iot-lab/catimex-power-monitoring/legacy/v0.1/boards/pcb/lmp2011/README.md

#PCB eagle schematics and boards for LMP2011

El LMP2011 es un OP AMP auto-zero de offset de entrada de 60uV máximo (en todo rango de temperatura) y 0.8 uV tipicos. Ademas tiene un CMRR tipico de 130dB con un minimo de  95dB.

### Cómo usar

Considerando que se tiene una placa compatible con RIOT:

- Conectar los controles de switch (SWITCH_CTRL_1 a SWITCH_CTRL_5) a GPIO.
- Conectar las salidas de low current, high current y adc volt (medición de supply) a las entradas analógicas.
- Conectar alimentación a entrada micro USB desde computadora o 5V.
- Conectar alimentación del MCU objetivo a VBAT. En caso de querer alimentar todo desde la alimentación USB, conectar un jumper entre 5V y VBAT.
- Si el MCU objetivo puede ser conectado por USB, utilizar el puerto USB tipo A. Este puerto mantiene la comunicación serial.
- En caso de no poder utilizar un USB, la alimentación del MCU objetivo puede obtenerse desde VMCU.

### Especificaciones:
- Alimentación de 5V desde USB
- Rango: ~10uA - 50mA
- Primera etapa ganancia de 100
- Segunda etapa amplifica 197 para bajas corrientes y 1.51 para altas corrientes.

### Working of current version (2) (detailed)

El funcionamiento de este circuito es equivalente al del MAX4239, sólo que sin un DC booster (falta verificar que efectivamente este no sea necesario).

La primera etapa se encarga de amplificar el voltage en la resistencia de Shunt mediante configuracion de amplificador diferencial. Las resistencias R1,R2,R4 y R5 conforman una ganancia diferencial de 100 (100k/1k) entre VBAT y VS- (terminales de la resistencia de shunt). R6 y C3 son añadidos para estabilidad, C3 además ayuda a disminuir los peaks de carga del auto-zero. C2 ayuda a mantener la fuente estable.

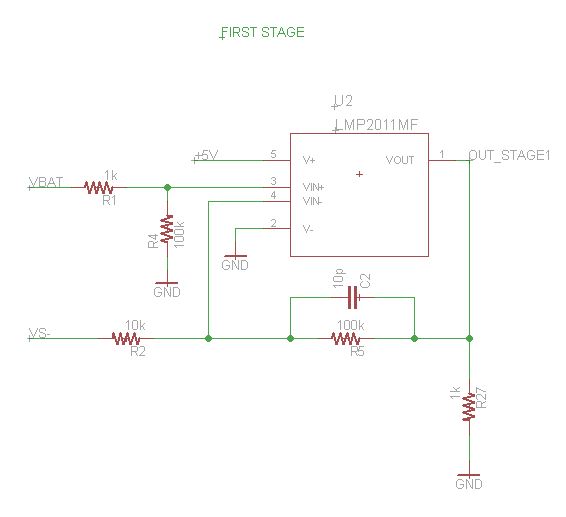
[picture p3: v0.1/boards/pcb/lmp2011/images/first.JPG]


La segunda etapa es conformada por un DUAL OP AMP LTC6241 de alta precision. Hay dos rangos de medicion que tienen distintas ganancias cada uno:
- Low current range: 0uA-600uA
- High current tange: 600uA-50mA

Para corrientes bajas, la segunda etapa amplifica x197. Para corrientes altas solo se amplifica x1.51. Estas ganancias acomodan el voltaje a los rangos del ADC. Las resistencias de 49.9R son utiles para aislar la salida del amplificador y evitar oscilaciones.

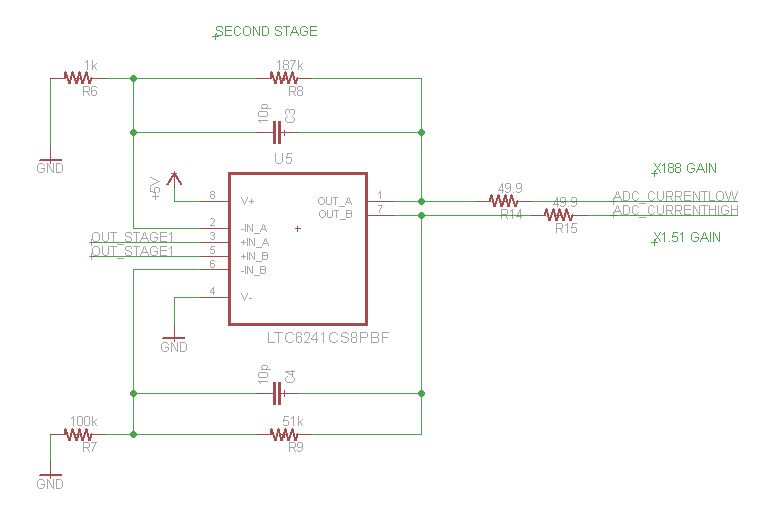
[picture p4: v0.1/boards/pcb/lmp2011/images/second.JPG]


Se utilizan 4 switch analogos normalmente abiertos para calibrar la medición en corrientes pequeñas utilizando las resistencias R9, R10, R13 y R14. Los TS5A23166DCUR son elegidos debido al alto voltaje soportado en sus entradas, alta corriente máxima y baja resistencia (0.7 omhs aprox.). En cambio, se elige un switch normalmente cerrado para la alimentación del MCU objetivo, un TS5A23167DCUR, de características equivalentes al TS5A23166DCUR. El capacitor C1 es puesto entre la alimentación del MCU objetivo para asegurar estabilidad.

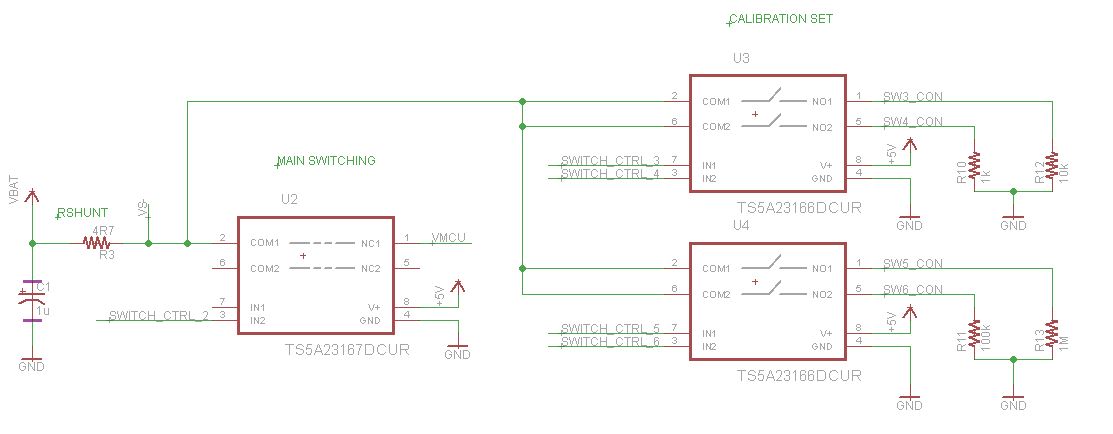
[picture p5: v0.1/boards/pcb/lmp2011/images/switch.JPG]


La etapa de buffer para la fuente de poder utiliza un LTC6240 de alta precision, configurado a ganancia x0.5 con tal de evitar que valores altos de voltajes no puedan ser leidos por ADC de referencias de voltaje bajo (5V fuente -> 2.5V ADC puede ser leido con referencia de 3.3V). Además permite aislar el nodo del ADC.

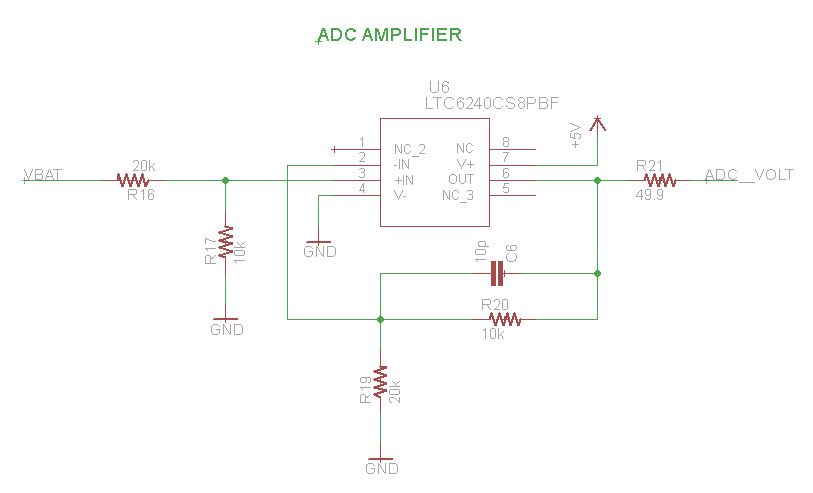
[picture p6: v0.1/boards/pcb/lmp2011/images/supply.JPG]


Para la alimentación, se utiliza una entrada micro USB tipo B hembra, que proporciona 5V desde una computadora o cargador. En caso de uso con la computadora, se han cortocircuitados las líneas de datos D+ y D-. Para evitar el ruido de alta frecuencia del computador, se utiliza una ferrita de alta impedancia a baja frecuencia (1K@1Mhz). Un conector hembra USB tipo A proporciona la salida del circuito para alimentar al MCU objetivo. Finalmente, se separa la tierra virtual de la digital mediante diodos schottky CUS08F30 debido a su rápida respuesta y bajo voltaje de activación.

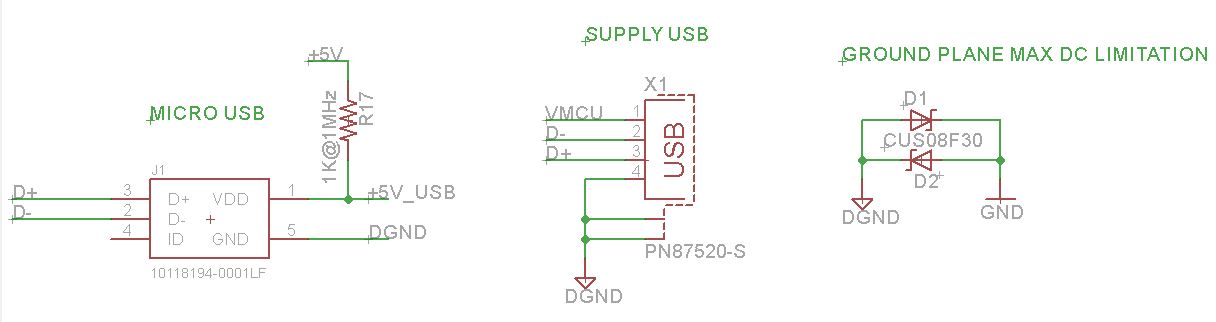
[picture p7: v0.1/boards/pcb/lmp2011/images/USB.JPG]


Diversos pines de utilidad son puestos a disposición del usuario. Estos permiten alimentar con fuente externa, observar las salidas de las distintas etapas, controlar switchs, etc. Las resistencias 21 a 25 son de pull down.

- SWITCH_CTRL_1: controla apertura del switch que proporciona energia al MCU.
- SWITCH_CTRL_2 a 5: controla cierre de switch a resistencias de calibracion.
- ADC_VOLT: salida buffer supply.
- VMCU: voltaje que se entrega al MCU objetivo. En corto circuito con el usb.
- GND: tierra
- OUT_STAGE1: salida primera etapa correinte.
- VS-: pata negativa resistencia de shunt.
- VBAT: voltaje con el que se supone se alimenta el MCU.
- +5V: salida de 5V, separada de USB por la ferrita.

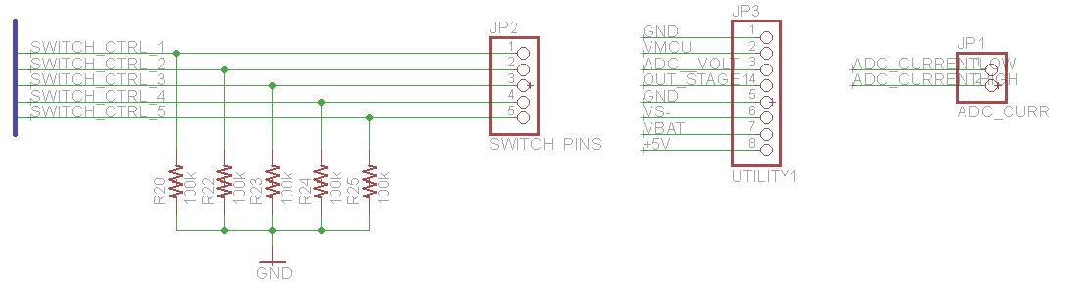
[picture p8: v0.1/boards/pcb/lmp2011/images/utility.JPG]


# Versiones placas

## LMP2011 V1 (prototipada)
Esta versión de la placa fue prototipada. La PCB fue manufacturada por OSHPARK y los componentes fueron comprados en DigiKey. El soldado de componentes y pruebas de laboratorio fueron realizados en el IOT LAB de Inria Chile.

### Acerca de

Esta versión de la placa considera una alimentación de 5V para todos los IC, excepto el LMP2011 que se le alimenta con 8V68 proporcionados por un DC booster.

La primera etapa es un amplificador diferencial de ganancia 10. La segunda etapa consta de los rango Low Current (ganancia de 19,7) y high current (ganancia de 1,51).

Para lecturas de la alimentacion del MCU objetivo, se utiliza una etapa que reduce el voltage a la mitad.

Tierras digital y analoga son separadas con diodos schottky.

Fuente de 5v de USB es filtrada con ferrita 1k@1MHz.

La carcasa del USB tipo A es conectado a tierra digital.

### Conclusiones a partir del prototipado de la placa

#### Observaciones
- Placa manufacturada
- Soldado de componentes OK
- Todos los IC reciben alimentación debida.
- Todos los IC reciben tierra debida.
- Re leyendo el datasheet, se observa que el LMP2011 no puede funcionar con 8v68. No se conecta el MIC2250 y en la salida de 8v68 se conectan los 5V.
- No se ha observado mediciones que sean concluyentes. Se ve que el LMP no funciona como debería. Se prueba en protoboard utilizando breakout y tampoco se observan buenos resultados.

#### Qué falta hacer
- Checkear que LMP2011 esté bien conectado y funcione como deba.
- Checkear el rango efectivo de medición.
- Realizar medición con microcontrolador. Que este haga la calibración y controle los switches.

#### Issues
- Problemas con el LMP2011
- La ganancia de la etapa de low current debiese ser 187, no 19,7. Esto fue debido a que la resistencia de 10K es incorrecta, debiese ser de 1K.
- Los switch de control de alimentación al MCU están mal conectados. Esto fue solucionado soldando un cable a las patas que lo controlan.
- Agregar resistencias de pulldown a los controles de los switch como precaución en caso de no existir.
- En la placa, hay nombres en la silkscreen cambiados.
- Con respecto al laboratorio: muchos problemas de estática, ocurrieron muchos casos de descarga electroestática que producían oscilaciones en el circuito y que podrían dañar a IC. El osciloscopio tiene un problema, en cierto momento se detiene y debe ser reiniciado, al momento de reiniciarse el canal 1 siempre ponía impedancia de 50ohm e invertido, afectando la observación.

#### Qué se podría mejorar
- Mejorar CMRR incrementando tolerancia de TODAS las resistencias, que sean de 0,1% o menos. También puede incrementarse aumentando la ganancia diferencial, pero esto afecta los rangos de medición.
- Los micro USB ojalá que sean Thru-hole para evitar que se salgan.
- Para el switch que entrega alimentación al MCU objetivo, unir los dos switch y así permitir más paso de corriente.

#### Tips
- Uso de pasta de soldar y pistola de calor es recomendable para componentes de tamaño muy reducido
- Cautín de punta plana y malla de cobre con flux ayuda a remover exceso de estaño
- USB thru-hole ojalá soldar con estaño de alto punto de fusión pues es más duro
- Descarga a tierra puede hacerse con salida a tierra de los equipos

## LMP2011 V2 (no prototipada)

Esta versión debiese solucionar todos los issues presentados en la versión anterior.
- Se quita el DC booster. Falta verificar que la alimentación sea correcta, quizás pueda volver a ocurrir el problema que surge en el MAX4239 con que las entradas no pueden estar a un valor tan cercano de la alimentación.
- La ganancia de low current es solucionada cambiando la resistencia de 10K por 1K.
- Los switch están bien conectados y reorganizados.
- Se incluyen resistencias de pull-down en las lineas de control de los switch.

La placa aún no se ha diseñado, sólo está el esquemático.
