iot-lab/catimex-power-monitoring/v0.2/ltspice/cm_ad4522_A.asc

C1: cap; .1µ
C2: cap; .1µ
C3: cap; .1µ
C4: cap; 1n
C5: cap; 1n
IMCU: current; 1µ; AC 1
R1: res; 10k
R2: res; 10k
R3: res; 1; tol=0.01 pwr=100m
R4: res; 200
R5: res; 10k
R6: res; 10k
R7: res; 10k
R8: res; 1k; tol=0.01 pwr=100m
R9: res; 10k
R10: res; 1k
R11: res; 1k
R12: res; 100k
R13: res; 100k
R14: res; 1k; tol=0.01 pwr=100m
R15: res; 10k
R16: res; 0
U1: ADA4522
U2: ADA4522
U3: ADA4522
U4: ADA4522
V1: voltage; 5
V2: voltage; -4.5
V3: voltage; {V_BAT_P}
Named nets: 0, Vcc, VBAT, Vee, S1_OUT
.step param V_BAT_P 2.5 3.0 0.1
.param V_BAT_P 4
.dc IMCU 0 250u 0.001u
High Precision
Mid/High Precision
.ac dec 10 1 1G
CM near to 0
Mid/High Precision
SUG: 2 0 ohm resistor to connect to Vee or GND
Higher PSRR and CMRR in single SUPPLY
Pre-ADC output filter, low pass sallen Key 2nd order 10kHz.
I_R4_max=0.5mA
x100 Gain
x100 Gain
