iot-lab/catimex-power-monitoring/v0.2/ltspice/cm_ada4522/cm_AD8629.asc

C1: cap; 10µ
C2: cap; 10µ
C3: cap; 0.1µ
C4: cap; 0.1µ
C5: cap; 10µ
C6: cap; 0.1µ
C7: cap; 0.1µ
C9: cap; 10n
C10: cap; 1n
C11: cap; 1n
C12: cap; 0.1µ
I1: current; 1m
R1: res; 1; tol=.1
R2: res; 200; tol=.1
R3: res; 100; tol=.1
R4: res; 20k; tol=.01
R5: res; 200; tol=.1
R6: res; 20k; tol=.01
R7: res; 12k
R8: res; 100; tol=.1
R9: res; 100; tol=.1
R10: res; 12k
R11: res; 508; tol=0.1
R12: res; 100k
R13: res; 100k
R14: res; 1k
R15: res; 2k
R16: res; 100k
U1: AD8629
U2: AD8629
U3: AD8629
U4: AD8422
U5: AD8629
V1: voltage; 5
V2: voltage; 8
V3: voltage; 8
V4: voltage; 5.5
Named nets: 0, Vcc+, Vbat, Vs, +5.5, Vcc-, V_low, V-high
.dc I1 1u 1000u 0.5u
x40Gain
TODO: Voltage 5.5V AD8629
TODO: Voltage 8V AD8422
