iot-lab/catimex-power-monitoring/v0.2/ltspice/cm_ltc6102/cm_ltc6102_ada4582_B.asc

C1: cap; 1n
C2: cap; 10p
C3: cap; .1µ
C4: cap; 100n
C6: cap; 1n
IMCU: current; 0
R1: res; 10; tol=.1
R2: res; 6.2k
R3: res; 1; tol=0.01 pwr=100m
R4: res; 10k; tol=.1
R5: res; 90k
R6: res; 10k
R7: res; 120
R10: res; 9; tol=.1
U1: LTC6102
U2: ADA4528
V1: voltage; 5
V3: voltage; {V_BAT_P}
Named nets: 0, Vcc, VBAT, S1_OUT, S2_OUT
.step param V_BAT_P 2.5 3.0 0.1
.param V_BAT_P 4
.dc IMCU 0 50u 0.001u
2nd Order Low Pass 10Khz Filter
1st Stage x1000 gain, LTC6102 High Side Current Sense
2nd Stage x100 gain,  ADA4528 Opamp
There is no need for very low output votage in second stage since we will have the amplified first stage voltage offset
