iot-lab/catimex-power-monitoring/v0.2/ltspice/cm_ltc6102/sallen_key.asc

C2: cap; 1n
C3: cap; 1n
R2: res; 10k
R5: res; 10k
R6: res; 10k
U1: ADA4522
V1: voltage; 5
V2: voltage; 1; AC 1
V3: voltage; -5
Named nets: Vcc, 0, Vee
.ac dec 10 1 1g
Second order sallen key low pass filter, 10Khz
Sallen key has a very low near 0 output impedance at DC
